antmicro/ov5640-dual-camera-board/assets/previews/layer0.png

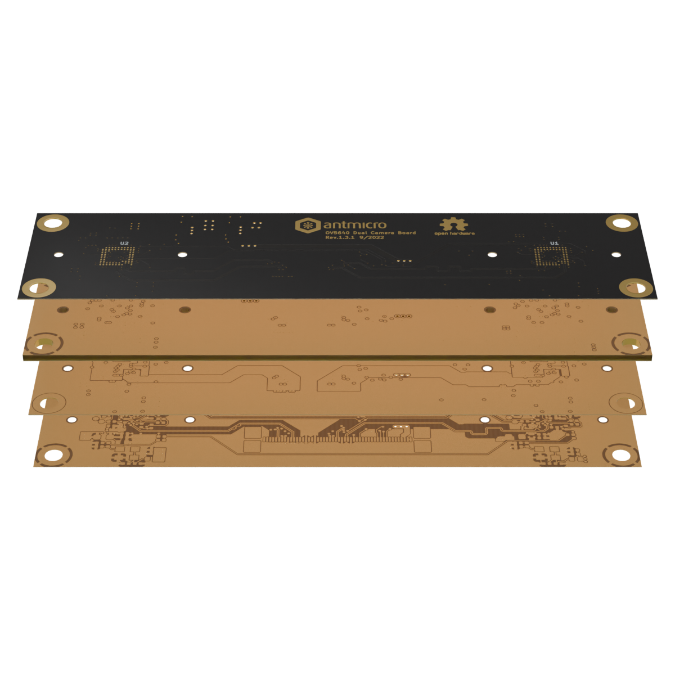
assets/previews/layer0.png
