antmicro/ov5640-dual-camera-board/assets/previews/layer1_thumbnail.png

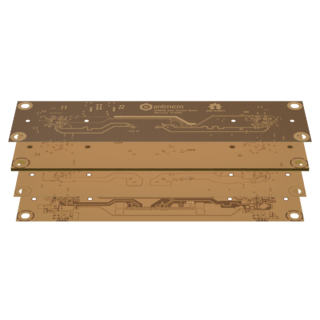
assets/previews/layer1_thumbnail.png
