antmicro/ov5640-dual-camera-board/assets/previews/layer2.png

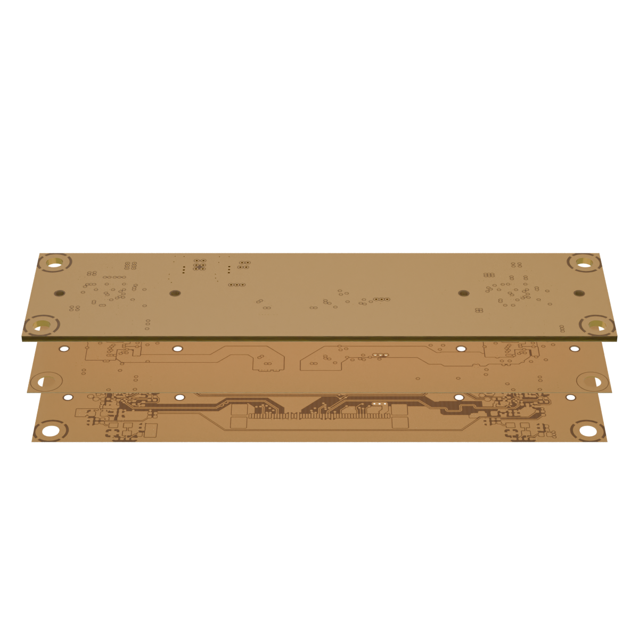
assets/previews/layer2.png
