antmicro/ov5640-dual-camera-board/assets/previews/layer3.png

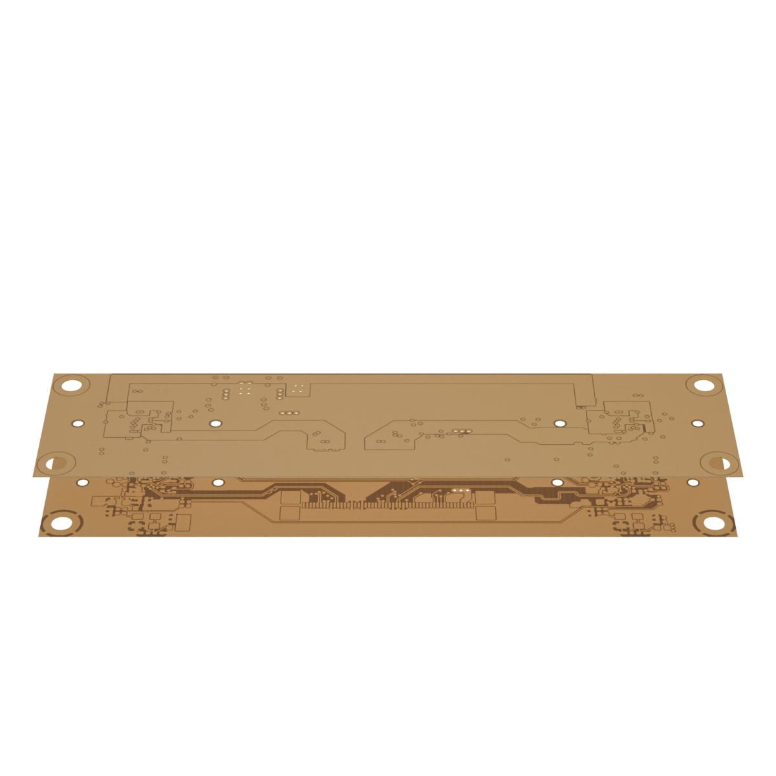
assets/previews/layer3.png
