antmicro/ov5640-dual-camera-board/assets/previews/layer4.png

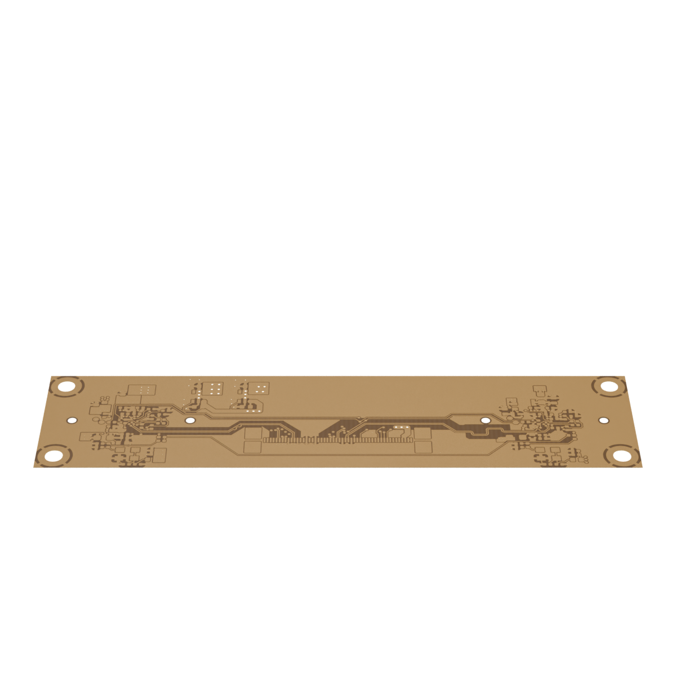
assets/previews/layer4.png
