antmicro/ov5640-dual-camera-board/assets/previews/leftB.png

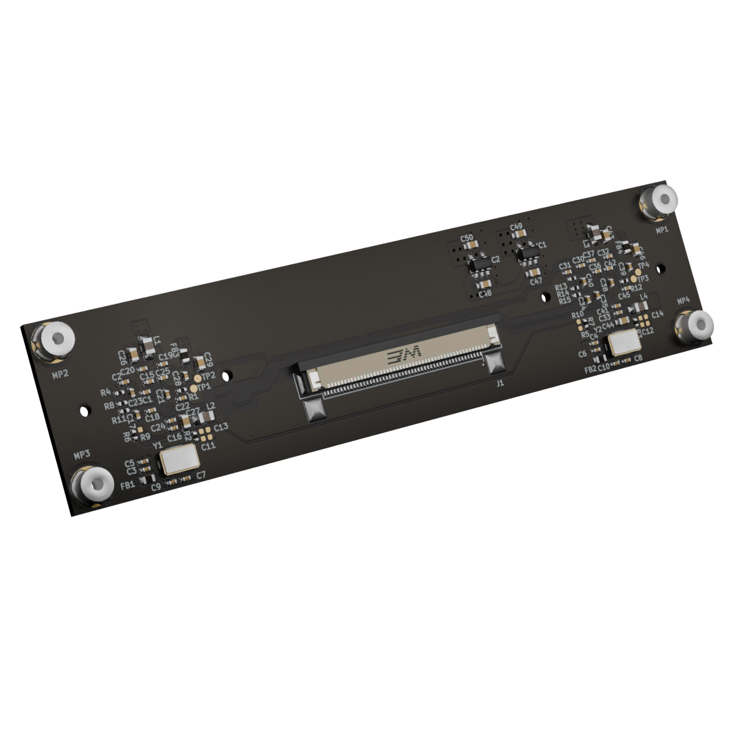
assets/previews/leftB.png
