antmicro/ov5640-dual-camera-board/assets/previews/orthoB.png

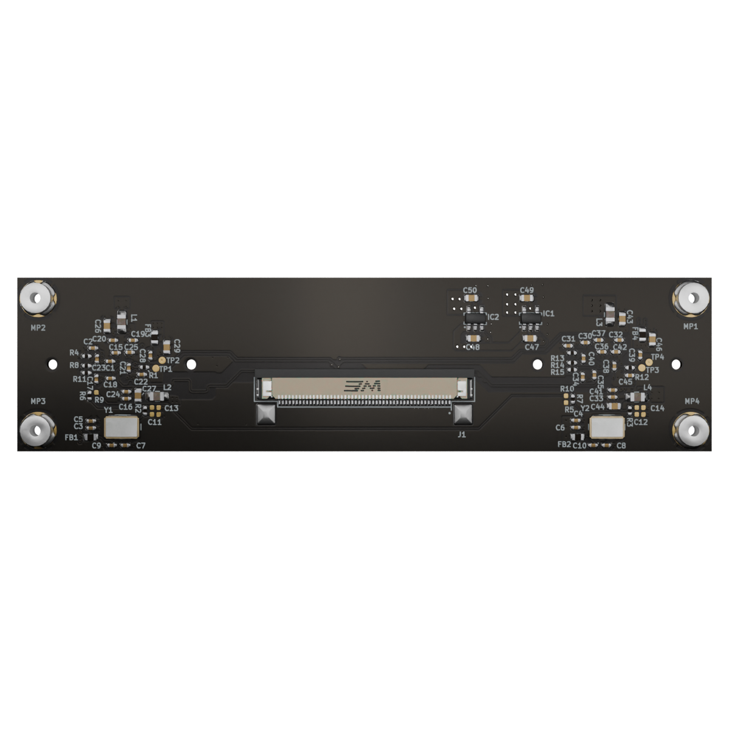
assets/previews/orthoB.png
