antmicro/ov5640-dual-camera-board/assets/previews/rightB.png

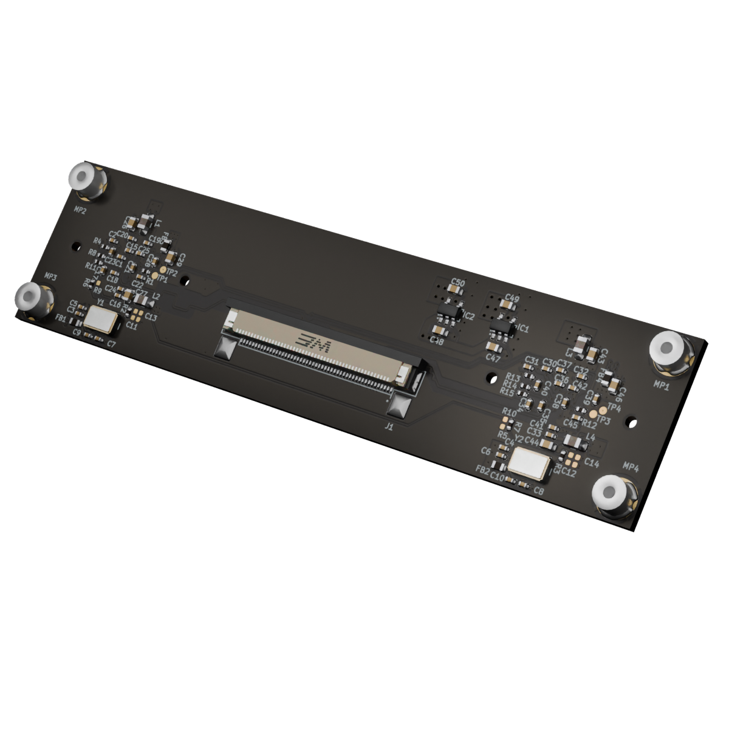
assets/previews/rightB.png
