antmicro/ov5640-dual-camera-board/assets/wireframe/wireframe_descriptions_bottom.png

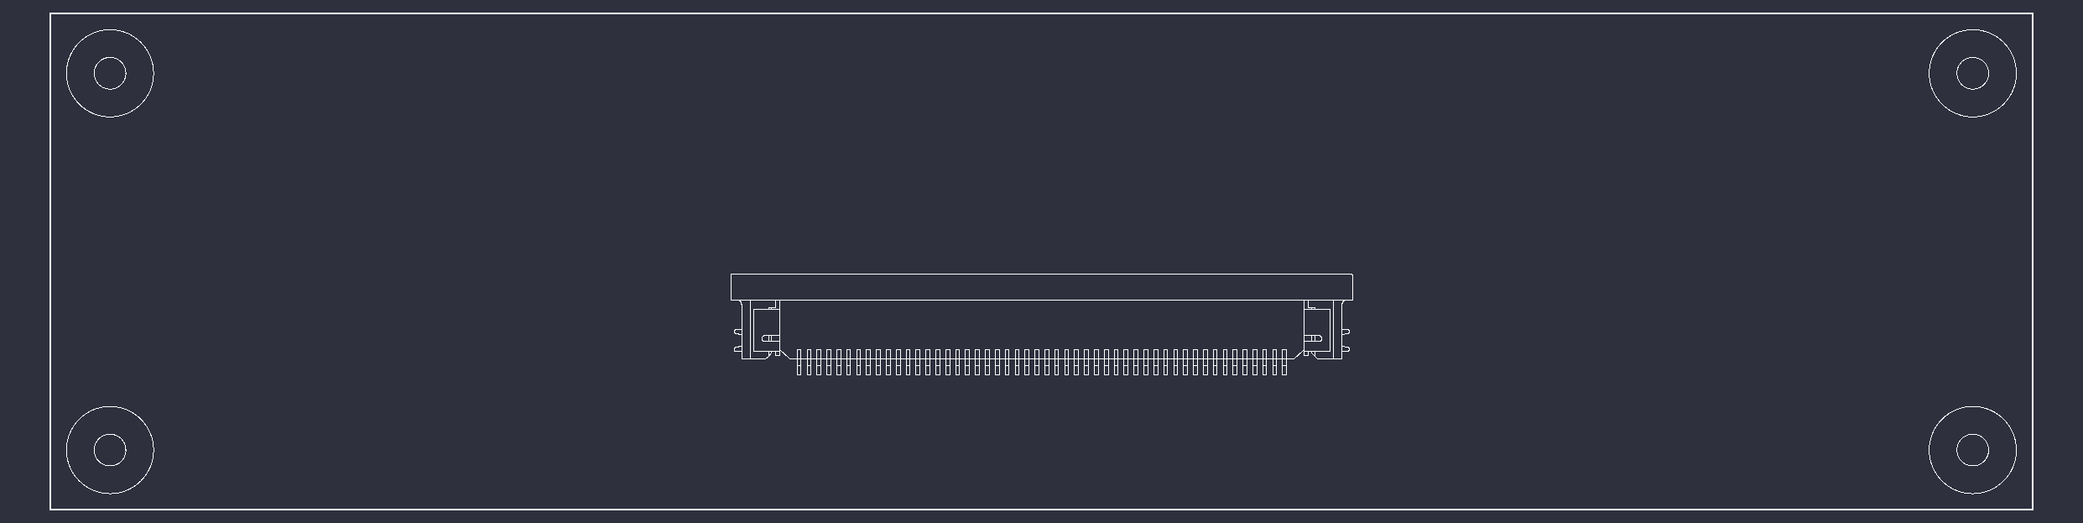
assets/wireframe/wireframe_descriptions_bottom.png
