antmicro/ov5640-dual-camera-board/assets/wireframe/wireframe_dimensions.png

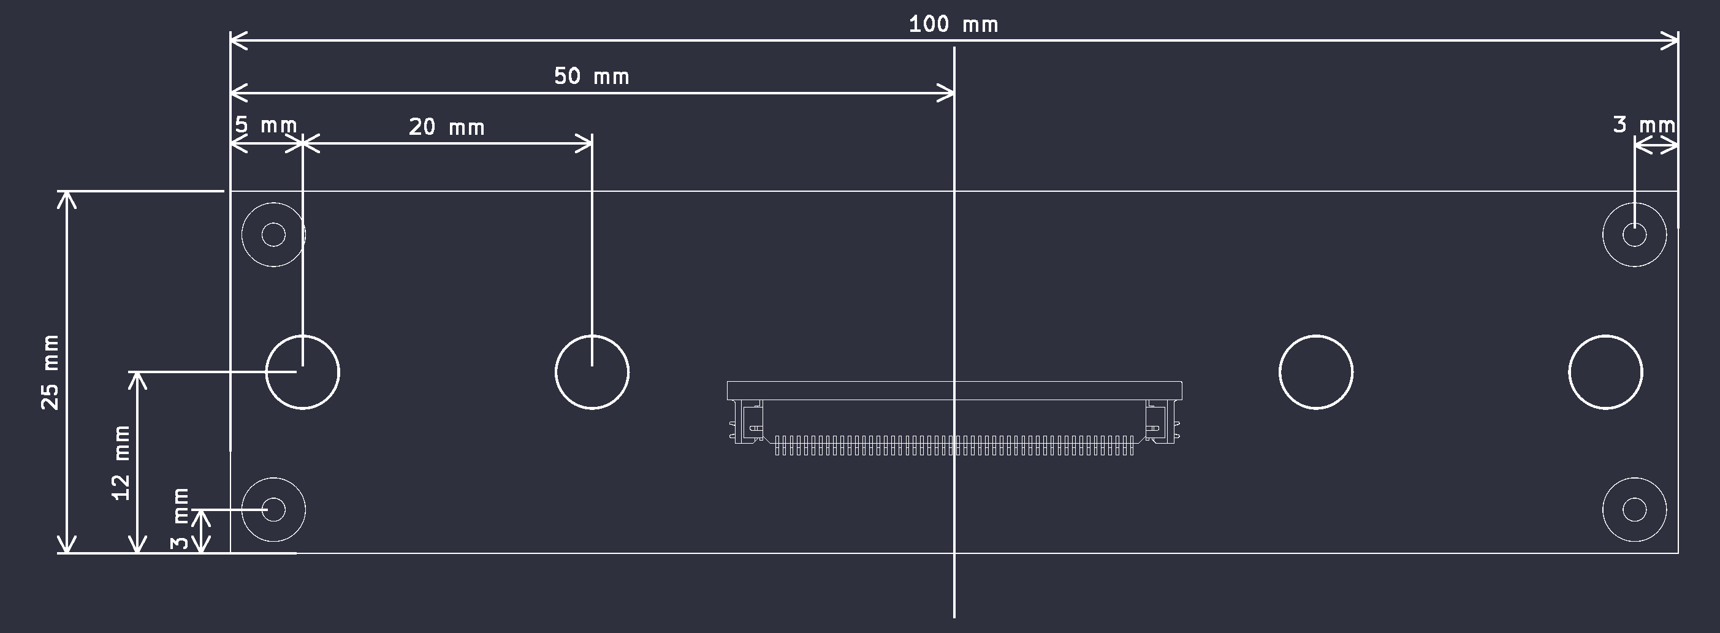
assets/wireframe/wireframe_dimensions.png
